CREPP-PLOEMEUR/Capteur_pollution_atmospherique/Images/800px-Surveillez_vos_particules_fines_Capture_d_e_cran_2_002.png

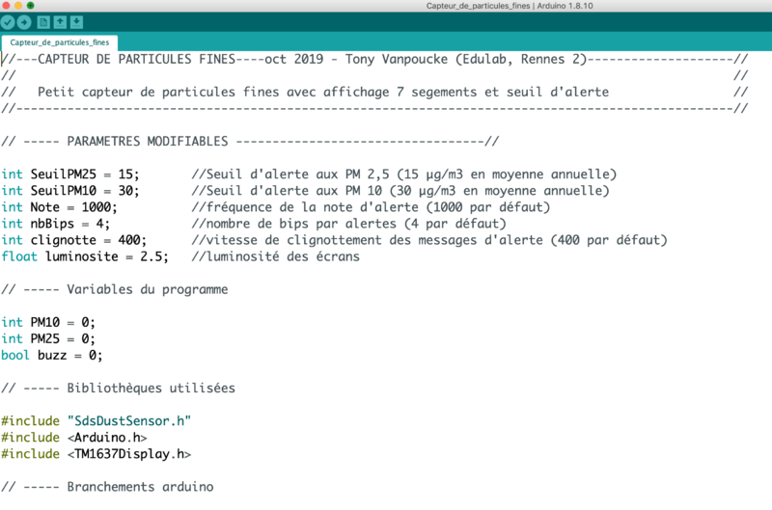
Images/800px-Surveillez_vos_particules_fines_Capture_d_e_cran_2_002.png
