CREPP-PLOEMEUR/Capteur_pollution_atmospherique/Images/800px-Surveillez_vos_particules_fines_IMG_2854.JPG

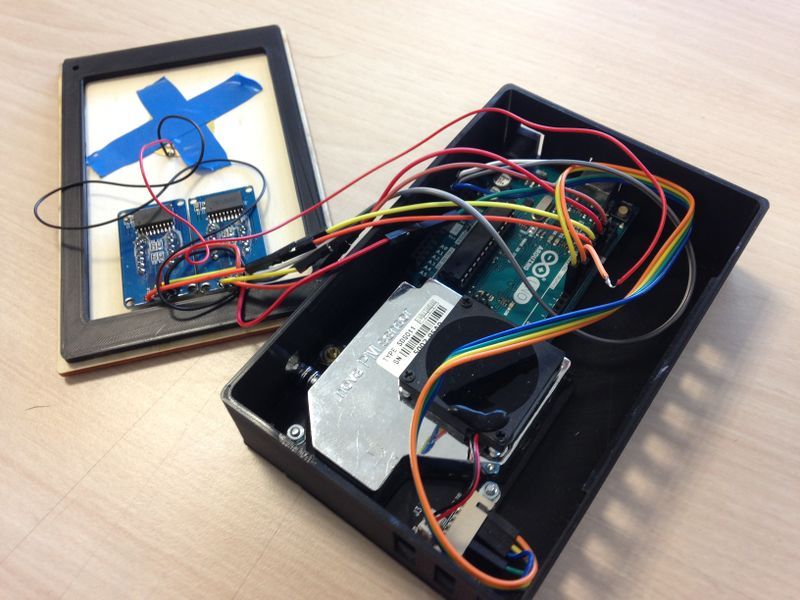
Images/800px-Surveillez_vos_particules_fines_IMG_2854.JPG
