CREPP-PLOEMEUR/Capteur_pollution_atmospherique/Misc/Surveillez vos particules fines Capture d e cran 2019-12-11 a 21.08.28 - Surveillez vos particules fines — Wikifab_fichiers/Etalonnage paramètres ajustables.png

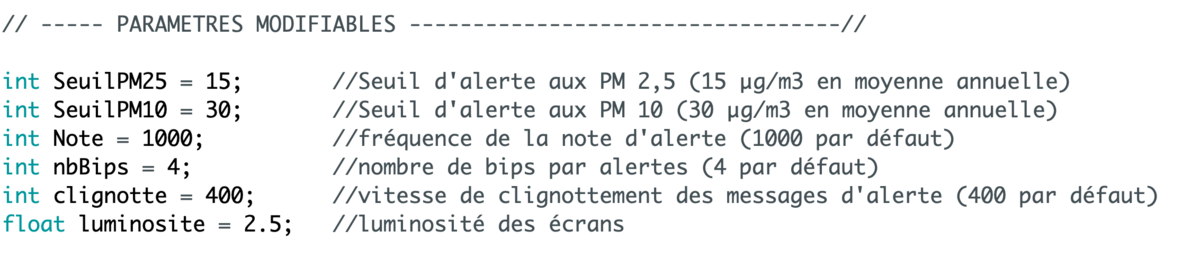
Misc/Surveillez vos particules fines Capture d e cran 2019-12-11 a 21.08.28 - Surveillez vos particules fines — Wikifab_fichiers/Etalonnage paramètres ajustables.png
