CREPP-PLOEMEUR/Capteur_pollution_atmospherique/Misc/Surveillez vos particules fines Capture d e cran 2019-12-11 a 21.08.28 - Surveillez vos particules fines — Wikifab_fichiers/ia-3d24b2f349bd2c07fff4b13d7a0d3904-px-Surveillez_vos_partic.png

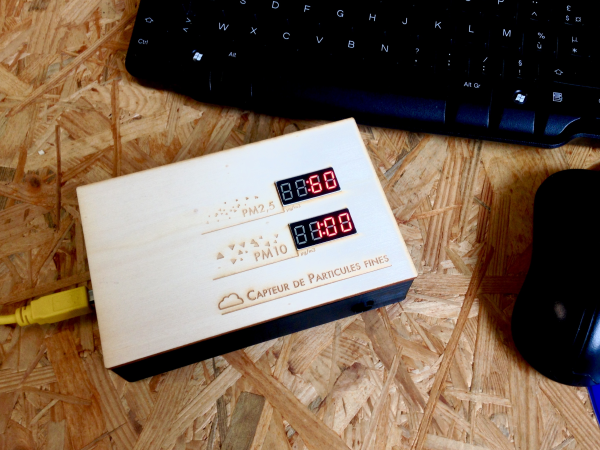
Misc/Surveillez vos particules fines Capture d e cran 2019-12-11 a 21.08.28 - Surveillez vos particules fines — Wikifab_fichiers/ia-3d24b2f349bd2c07fff4b13d7a0d3904-px-Surveillez_vos_partic.png
